PhysicsDptAngers/polyUAnalog/hardware/FX/img/PCM5102a.jpeg

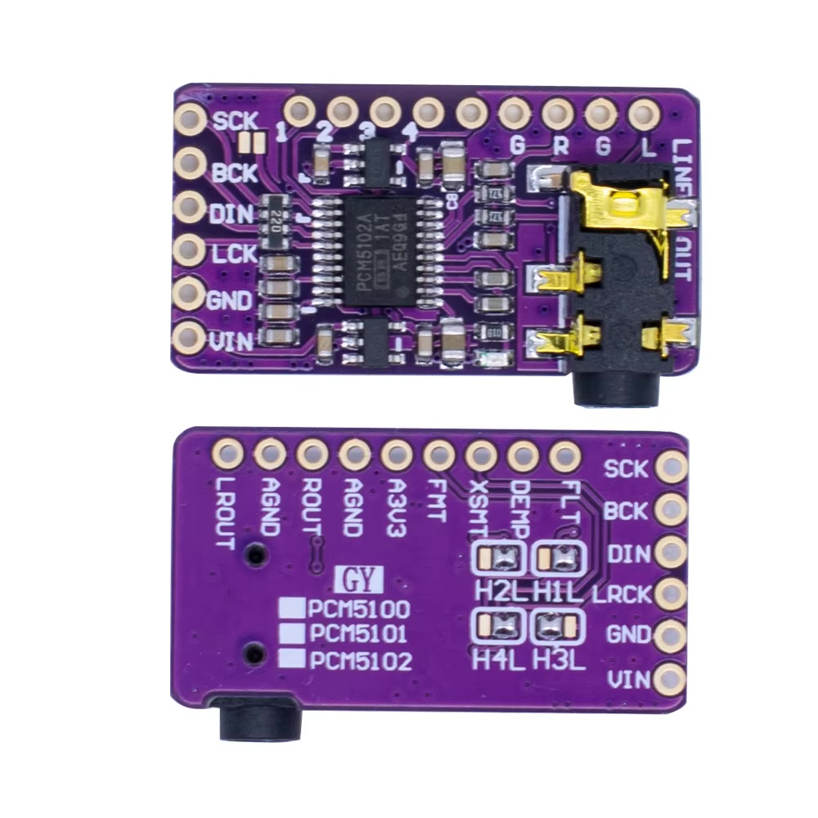
hardware/FX/img/PCM5102a.jpeg
