PhysicsDptAngers/polyUAnalog/hardware/voice/doc/img/Falstad_Balance_cv_level_shifter.png

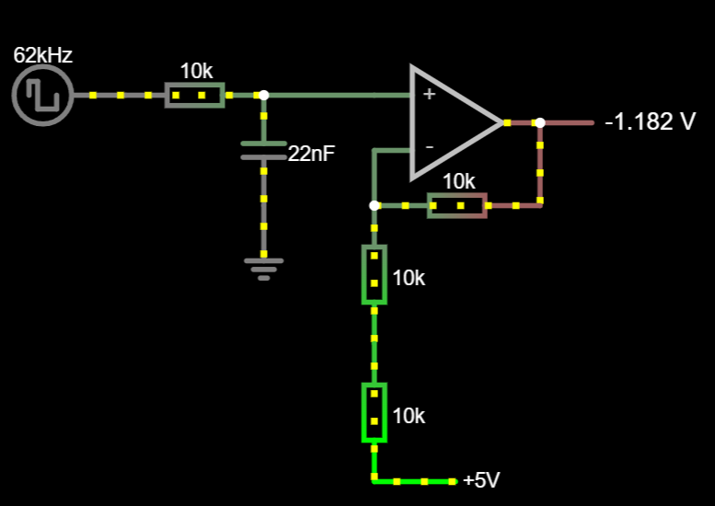
hardware/voice/doc/img/Falstad_Balance_cv_level_shifter.png
