PhysicsDptAngers/polyUAnalog/hardware/voice/doc/img/Wave_select_schematics.png

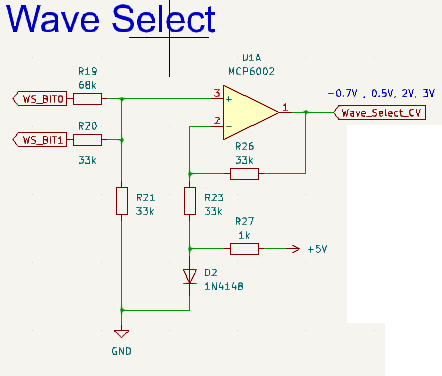
hardware/voice/doc/img/Wave_select_schematics.png
