PhysicsDptAngers/polyUAnalog/resources/conductor_board.png

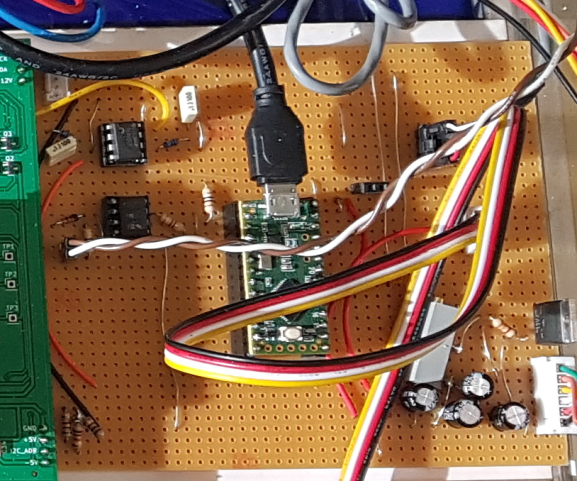
resources/conductor_board.png
