PhysicsDptAngers/polyUAnalog/resources/Photo_arch_main.png

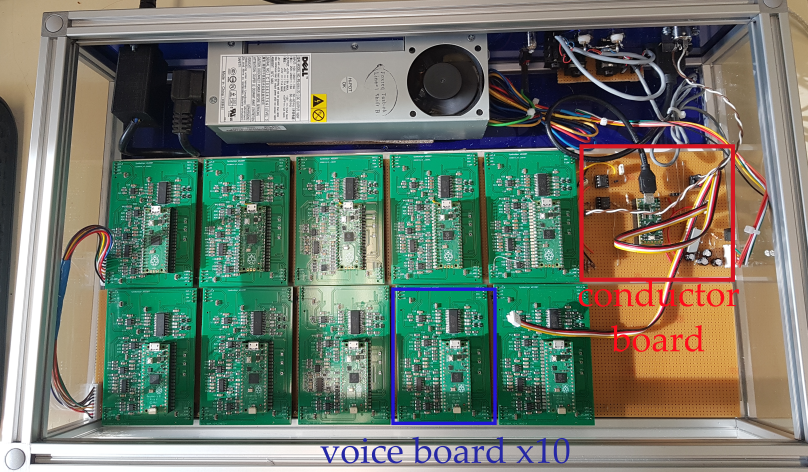
resources/Photo_arch_main.png
