PhysicsDptAngers/polyUAnalog/resources/photo_voice.png

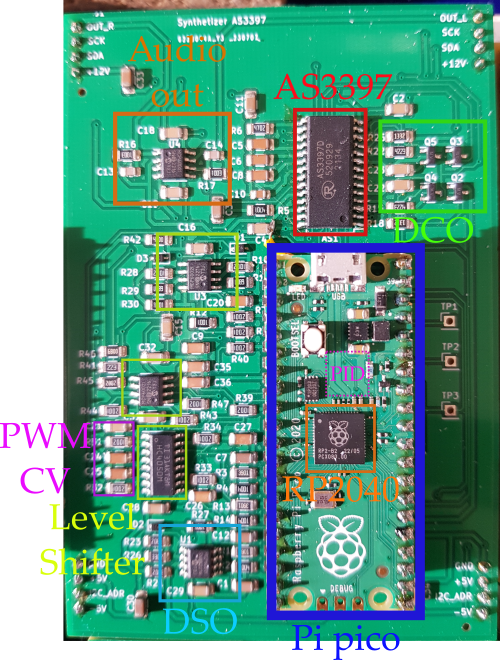
resources/photo_voice.png
