PhysicsDptAngers/polyUAnalog/resources/schema_AS3397.png

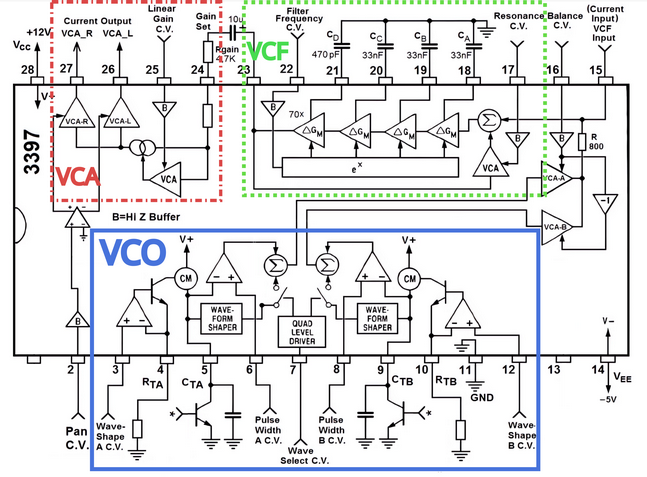
resources/schema_AS3397.png
