PhysicsDptAngers/polyUAnalog/resources/voice_archi.png

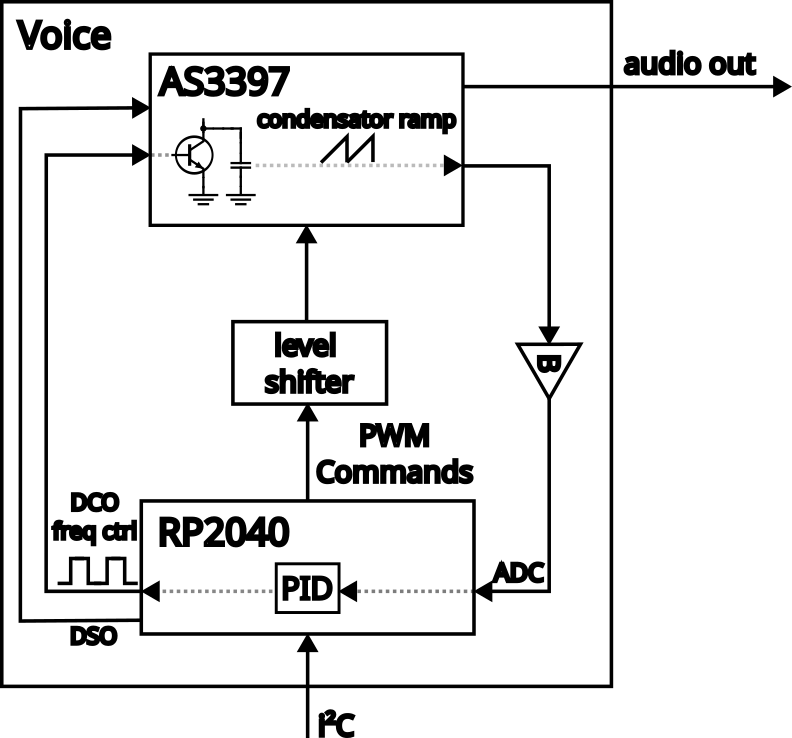
resources/voice_archi.png
