PhysicsDptAngers/polyUAnalog/firmware/conductor/preset.h

#ifndef PRESET_H
#define PRESET_H

//OSCILLATOR 1
#define OSC1WAVE 9
#define OSC1TRANSPOSE 10
#define OSC1PWM 11
#define OSC1DETUNE 18

//OSCILLATOR 2
#define OSC2WAVE 12
#define OSC2TRANSPOSE 13
#define OSC2DETUNE 14
#define OSC2PWM 15

//MIXER
#define BALANCE 16

//DSO
#define DSOWAVE 38
#define DSOTRANSPOSE 39
#define DSODETUNE 40
#define DSOPW 41
#define DSOMIX 42
#define MIXNOISE 44

//ENVELOPPE GENERATOR 1
#define EG1ATTACK 19
#define EG1DECAY 20
#define EG1SUSTAIN 21
#define EG1RELEASE 22
//ENVELOPPE GENERATOR 2
#define EG2ATTACK 23
#define EG2DECAY 24
#define EG2SUSTAIN 25
#define EG2RELEASE 26
#define EG22FREQ 51

//LOW PASS FILTER
#define FILTERFC 74
#define FILTERFCLOW 75
#define FILTERRES 27
#define FILTERKEY 28
#define FILTERENV 29
#define MODAMOUNT 37

//LOW FREQUENCY OSCILLATOR 1
#define LFO1WAVE 30
#define LFO1FREQ 31
#define LFO12PWA 35
#define LFO12PWB 36
#define LFO12FREQ 85
#define LFO12FILTER 86
#define LFO12PWDSO 43
#define LFO12PAN 45

//Velocity
#define VEL2VCA 46
#define VEL2FILTER 47

//Pan
#define KEY2PAN 48

//After Touch
#define AFT2VCA 49
#define AFT2FILTER 50

//GLOBAL PARAMETERS
#define GLBDETUNE 104
#define GLBTRANSPOSE 105
#define GLBVELOCITY 106
#define GLBVOLUME 7
#define GLBGLIDE 5
#define PAN 32

#define ALLSOUNDOFF 120
#define ALLNOTESOFF 123

// Definition of MIDI controller names
const char* controlleurNom[] = {
  "OSC1WAVE", "OSC1TRANSPOSE", "OSC1PWM", "OSC1DETUNE",
  "OSC2WAVE", "OSC2TRANSPOSE", "OSC2DETUNE", "OSC2PWM",
  "BALANCE",
  "DSOWAVE", "DSOTRANSPOSE", "DSODETUNE", "DSOPW", "DSOMIX", "MIXNOISE",
  "EG1ATTACK", "EG1DECAY", "EG1SUSTAIN", "EG1RELEASE",
  "EG2ATTACK", "EG2DECAY", "EG2SUSTAIN", "EG2RELEASE", "EG22FREQ",
  "FILTERFC", "FILTERFCLOW", "FILTERRES", "FILTERKEY", "FILTERENV", "MODAMOUNT",
  "LFO1WAVE", "LFO1FREQ", "LFO12PWA", "LFO12PWB", "LFO12FREQ", "LFO12FILTER", "LFO12PWDSO", "LFO12PAN",
  "VEL2VCA", "VEL2FILTER",
  "KEY2PAN",
  "AFT2VCA", "AFT2FILTER",
  "GLBDETUNE", "GLBTRANSPOSE", "GLBVELOCITY", "GLBVOLUME", "GLBGLIDE", "PAN"
};

// Setting MIDI controller numbers
const byte controlleurNum[] = {
  OSC1WAVE, OSC1TRANSPOSE, OSC1PWM, OSC1DETUNE,
  OSC2WAVE, OSC2TRANSPOSE, OSC2DETUNE, OSC2PWM,
  BALANCE,
  DSOWAVE, DSOTRANSPOSE, DSODETUNE, DSOPW, DSOMIX, MIXNOISE,
  EG1ATTACK, EG1DECAY, EG1SUSTAIN, EG1RELEASE,
  EG2ATTACK, EG2DECAY, EG2SUSTAIN, EG2RELEASE, EG22FREQ,
  FILTERFC, FILTERFCLOW, FILTERRES, FILTERKEY, FILTERENV, MODAMOUNT,
  LFO1WAVE, LFO1FREQ, LFO12PWA, LFO12PWB, LFO12FREQ, LFO12FILTER, LFO12PWDSO, LFO12PAN,
  VEL2VCA, VEL2FILTER,
  KEY2PAN,
  AFT2VCA, AFT2FILTER,
  GLBDETUNE, GLBTRANSPOSE, GLBVELOCITY, GLBVOLUME, GLBGLIDE, PAN
};

#define NBPARAM 102

//Preset format {MIDI_CONTROLEUR, Value, MIDI_CONTROLEUR, Value, ...}
const uint8_t Saw0[] = { OSC1WAVE, 1, OSC1TRANSPOSE, 64, OSC1PWM, 64, OSC1DETUNE, 64,
                         OSC2WAVE, 1, OSC2TRANSPOSE, 64, OSC2DETUNE, 64, OSC2PWM, 64,
                         BALANCE, 0,
                         DSOWAVE, 0, DSOTRANSPOSE, 64, DSODETUNE, 64, DSOPW, 64, DSOMIX, 0, MIXNOISE, 0,
                         EG1ATTACK, 1, EG1DECAY, 127, EG1SUSTAIN, 127, EG1RELEASE, 1,
                         EG2ATTACK, 1, EG2DECAY, 127, EG2SUSTAIN, 127, EG2RELEASE, 1, EG22FREQ, 0,
                         FILTERFCLOW, 63, FILTERFC, 106, FILTERRES, 63, FILTERKEY, 0, FILTERENV, 0, MODAMOUNT, 0,
                         LFO1WAVE, 0, LFO1FREQ, 16, LFO12PWA, 0, LFO12PWB, 0, LFO12FREQ, 0, LFO12FILTER, 0, LFO12PWDSO, 0, LFO12PAN, 0,
                         VEL2VCA, 127, VEL2FILTER, 0,
                         KEY2PAN, 0,
                         AFT2VCA, 0, AFT2FILTER, 0,
                         GLBDETUNE, 64, GLBTRANSPOSE, 64, GLBVELOCITY, 127, GLBVOLUME, 32, GLBGLIDE, 0, PAN, 64,
                         ALLSOUNDOFF, 1, ALLNOTESOFF, 0 };

const uint8_t Preset1[] = { OSC1WAVE, 0, OSC1TRANSPOSE, 64, OSC1PWM, 64, OSC1DETUNE, 64,
                            OSC2WAVE, 0, OSC2TRANSPOSE, 64, OSC2DETUNE, 65, OSC2PWM, 64,
                            BALANCE, 120, DSOWAVE, 0, DSOTRANSPOSE, 64, DSODETUNE, 64,
                            DSOPW, 64, DSOMIX, 0, MIXNOISE, 0, EG1ATTACK, 1,
                            EG1DECAY, 127, EG1SUSTAIN, 127, EG1RELEASE, 1, EG2ATTACK, 1,
                            EG2DECAY, 127, EG2SUSTAIN, 127, EG2RELEASE, 1, EG22FREQ, 0,
                            FILTERFC, 106, FILTERFCLOW, 63, FILTERRES, 4, FILTERKEY, 0,
                            FILTERENV, 0, MODAMOUNT, 0, LFO1WAVE, 0, LFO1FREQ, 30,
                            LFO12PWA, 57, LFO12PWB, 0, LFO12FREQ, 0, LFO12FILTER, 18,
                            LFO12PWDSO, 0, LFO12PAN, 6, VEL2VCA, 127, VEL2FILTER, 0,
                            KEY2PAN, 0, AFT2VCA, 0, AFT2FILTER, 0, GLBDETUNE, 64,
                            GLBTRANSPOSE, 64, GLBVELOCITY, 127, GLBVOLUME, 32, GLBGLIDE, 3, PAN, 64 };

const uint8_t Preset2[] = { OSC1WAVE, 1, OSC1TRANSPOSE, 64, OSC1PWM, 64, OSC1DETUNE, 64,
                            OSC2WAVE, 1, OSC2TRANSPOSE, 64, OSC2DETUNE, 65, OSC2PWM, 64,
                            BALANCE, 76, DSOWAVE, 0, DSOTRANSPOSE, 64, DSODETUNE, 64,
                            DSOPW, 64, DSOMIX, 0, MIXNOISE, 0, EG1ATTACK, 1,
                            EG1DECAY, 127, EG1SUSTAIN, 127, EG1RELEASE, 1, EG2ATTACK, 1,
                            EG2DECAY, 127, EG2SUSTAIN, 127, EG2RELEASE, 1, EG22FREQ, 0,
                            FILTERFC, 106, FILTERFCLOW, 63, FILTERRES, 17, FILTERKEY, 0,
                            FILTERENV, 0, MODAMOUNT, 0, LFO1WAVE, 0, LFO1FREQ, 15,
                            LFO12PWA, 0, LFO12PWB, 0, LFO12FREQ, 0, LFO12FILTER, 49,
                            LFO12PWDSO, 0, LFO12PAN, 14, VEL2VCA, 127, VEL2FILTER, 0,
                            KEY2PAN, 0, AFT2VCA, 0, AFT2FILTER, 0, GLBDETUNE, 64,
                            GLBTRANSPOSE, 64, GLBVELOCITY, 127, GLBVOLUME, 32, GLBGLIDE, 3, PAN, 64 };

const uint8_t Preset3[] = { OSC1WAVE, 0, OSC1TRANSPOSE, 64, OSC1PWM, 0, OSC1DETUNE, 64,
                            OSC2WAVE, 1, OSC2TRANSPOSE, 64, OSC2DETUNE, 65, OSC2PWM, 64,
                            BALANCE, 0, DSOWAVE, 0, DSOTRANSPOSE, 64, DSODETUNE, 64,
                            DSOPW, 64, DSOMIX, 0, MIXNOISE, 0, EG1ATTACK, 86,
                            EG1DECAY, 113, EG1SUSTAIN, 84, EG1RELEASE, 9, EG2ATTACK, 1,
                            EG2DECAY, 127, EG2SUSTAIN, 127, EG2RELEASE, 1, EG22FREQ, 0,
                            FILTERFC, 106, FILTERFCLOW, 63, FILTERRES, 22, FILTERKEY, 0,
                            FILTERENV, 0, MODAMOUNT, 0, LFO1WAVE, 0, LFO1FREQ, 25,
                            LFO12PWA, 96, LFO12PWB, 0, LFO12FREQ, 0, LFO12FILTER, 41,
                            LFO12PWDSO, 0, LFO12PAN, 0, VEL2VCA, 127, VEL2FILTER, 0,
                            KEY2PAN, 0, AFT2VCA, 0, AFT2FILTER, 0, GLBDETUNE, 64,
                            GLBTRANSPOSE, 64, GLBVELOCITY, 127, GLBVOLUME, 32, GLBGLIDE, 3, PAN, 64 };

const uint8_t Tri1[] = { OSC1WAVE, 2, OSC1TRANSPOSE, 52, OSC1PWM, 0, OSC1DETUNE, 64,
                         OSC2WAVE, 2, OSC2TRANSPOSE, 64, OSC2DETUNE, 66, OSC2PWM, 0,
                         BALANCE, 0, DSOWAVE, 0, DSOTRANSPOSE, 64, DSODETUNE, 64,
                         DSOPW, 64, DSOMIX, 0, MIXNOISE, 0, EG1ATTACK, 1,
                         EG1DECAY, 127, EG1SUSTAIN, 127, EG1RELEASE, 1, EG2ATTACK, 1,
                         EG2DECAY, 127, EG2SUSTAIN, 127, EG2RELEASE, 1, EG22FREQ, 0,
                         FILTERFC, 106, FILTERFCLOW, 63, FILTERRES, 4, FILTERKEY, 0,
                         FILTERENV, 0, MODAMOUNT, 0, LFO1WAVE, 0, LFO1FREQ, 16,
                         LFO12PWA, 0, LFO12PWB, 0, LFO12FREQ, 0, LFO12FILTER, 0,
                         LFO12PWDSO, 0, LFO12PAN, 0, VEL2VCA, 127, VEL2FILTER, 0,
                         KEY2PAN, 0, AFT2VCA, 0, AFT2FILTER, 0, GLBDETUNE, 64,
                         GLBTRANSPOSE, 64, GLBVELOCITY, 127, GLBVOLUME, 32, GLBGLIDE, 0, PAN, 64 };

const uint8_t Tri2[] = { OSC1WAVE, 3, OSC1TRANSPOSE, 64, OSC1PWM, 0, OSC1DETUNE, 64,
                         OSC2WAVE, 3, OSC2TRANSPOSE, 64, OSC2DETUNE, 66, OSC2PWM, 0,
                         BALANCE, 91, DSOWAVE, 0, DSOTRANSPOSE, 64, DSODETUNE, 64,
                         DSOPW, 64, DSOMIX, 0, MIXNOISE, 0, EG1ATTACK, 1,
                         EG1DECAY, 127, EG1SUSTAIN, 127, EG1RELEASE, 1, EG2ATTACK, 1,
                         EG2DECAY, 127, EG2SUSTAIN, 127, EG2RELEASE, 1, EG22FREQ, 0,
                         FILTERFC, 106, FILTERFCLOW, 63, FILTERRES, 4, FILTERKEY, 0,
                         FILTERENV, 0, MODAMOUNT, 0, LFO1WAVE, 0, LFO1FREQ, 16,
                         LFO12PWA, 0, LFO12PWB, 0, LFO12FREQ, 0, LFO12FILTER, 0,
                         LFO12PWDSO, 0, LFO12PAN, 0, VEL2VCA, 127, VEL2FILTER, 0,
                         KEY2PAN, 0, AFT2VCA, 0, AFT2FILTER, 0, GLBDETUNE, 64,
                         GLBTRANSPOSE, 64, GLBVELOCITY, 127, GLBVOLUME, 32, GLBGLIDE, 0, PAN, 64 };

const uint8_t Tri3[] = { OSC1WAVE, 4, OSC1TRANSPOSE, 64, OSC1PWM, 0, OSC1DETUNE, 64,
                         OSC2WAVE, 4, OSC2TRANSPOSE, 64, OSC2DETUNE, 66, OSC2PWM, 0,
                         BALANCE, 67, DSOWAVE, 0, DSOTRANSPOSE, 64, DSODETUNE, 64,
                         DSOPW, 64, DSOMIX, 0, MIXNOISE, 0, EG1ATTACK, 1,
                         EG1DECAY, 127, EG1SUSTAIN, 127, EG1RELEASE, 1, EG2ATTACK, 1,
                         EG2DECAY, 127, EG2SUSTAIN, 127, EG2RELEASE, 1, EG22FREQ, 0,
                         FILTERFC, 106, FILTERFCLOW, 63, FILTERRES, 4, FILTERKEY, 0,
                         FILTERENV, 0, MODAMOUNT, 0, LFO1WAVE, 0, LFO1FREQ, 16,
                         LFO12PWA, 0, LFO12PWB, 0, LFO12FREQ, 0, LFO12FILTER, 0,
                         LFO12PWDSO, 0, LFO12PAN, 0, VEL2VCA, 127, VEL2FILTER, 0,
                         KEY2PAN, 0, AFT2VCA, 0, AFT2FILTER, 0, GLBDETUNE, 64,
                         GLBTRANSPOSE, 64, GLBVELOCITY, 127, GLBVOLUME, 32, GLBGLIDE, 0, PAN, 64 };

const uint8_t Square1[] = { OSC1WAVE, 0, OSC1TRANSPOSE, 64, OSC1PWM, 127, OSC1DETUNE, 64,
                            OSC2WAVE, 0, OSC2TRANSPOSE, 64, OSC2DETUNE, 66, OSC2PWM, 127,
                            BALANCE, 127, DSOWAVE, 0, DSOTRANSPOSE, 64, DSODETUNE, 64,
                            DSOPW, 64, DSOMIX, 0, MIXNOISE, 0, EG1ATTACK, 1,
                            EG1DECAY, 127, EG1SUSTAIN, 127, EG1RELEASE, 1, EG2ATTACK, 1,
                            EG2DECAY, 127, EG2SUSTAIN, 127, EG2RELEASE, 1, EG22FREQ, 0,
                            FILTERFC, 106, FILTERFCLOW, 63, FILTERRES, 0, FILTERKEY, 0,
                            FILTERENV, 0, MODAMOUNT, 0, LFO1WAVE, 0, LFO1FREQ, 16,
                            LFO12PWA, 0, LFO12PWB, 0, LFO12FREQ, 0, LFO12FILTER, 0,
                            LFO12PWDSO, 0, LFO12PAN, 0, VEL2VCA, 127, VEL2FILTER, 0,
                            KEY2PAN, 0, AFT2VCA, 0, AFT2FILTER, 0, GLBDETUNE, 64,
                            GLBTRANSPOSE, 64, GLBVELOCITY, 127, GLBVOLUME, 32, GLBGLIDE, 0, PAN, 64 };

// Preset table
const uint8_t* Presets[] = { Saw0, Tri1, Tri2, Tri3, Square1, Preset1, Preset2, Preset3 /* Ajoutez d'autres tableaux de préréglages ici */ };
#endif
