PhysicsDptAngers/polyUAnalog/firmware/voice/as3397.h

#ifndef AS3397_H
#define AS3397_H

#include <math.h>
#include <hardware/gpio.h>
#include "hardware/pwm.h"
#include "hardware/adc.h"
#include "hardware/dma.h"
#include "pico/stdlib.h"
#include "hardware/pio.h"
#include "hardware/clocks.h"
#include "aspin.h"

#define PIDFIXE 1
#define ERROR_SUM_MAX 50000

const uint64_t srateFactor = 4294967296;
#if PIDFIXE == 1
const int64_t SCALE_FACTOR = 1 << 16;
#endif

const float MAXFREQ = 12544;
const float _div = 2;

const int CAPTURE_DEPTH = 100;
const float Fe = 1000000;

static int CAPTURE_CHANNEL = 0;
static uint16_t capture_buf[CAPTURE_DEPTH];
static uint dma_chan_adc;
static dma_channel_config cfg;

struct CallbackData {
  uint8_t WaveshapeFactor = 1;
  long SetPoint = WaveshapeFactor * 2.5 / convFactor;  // Initialise la consigne de l'asservissement à une amplitude de 2.5V
  long error = 0, output = 0;                          //Variables de la commande PI
  long errorSum[128] = {};
  uint8_t note;
#if PIDFIXE == 0
  float _Kp = 440 * Kp;
  float _Ki = Ki / 440;
#else
  int64_t _Kp = 440 * Kp * SCALE_FACTOR;
  int64_t _Ki = (Ki / 440) * SCALE_FACTOR;
#endif
  float noteFreq = 440;
  float noteDiv = 1;
  int64_t delay_us;
  uint32_t sliceH;
  uint32_t sliceL;
  uint32_t channelH;
  uint32_t channelL;
  int8_t Pwm;
  uint32_t PhaseAcc;
  uint32_t PhaseInc;

  long slope = 0;
  float Div = 0;
};

struct PWMsliceChannel {
  uint32_t slice;
  uint32_t channel;
  uint32_t dutyMax;
};


static struct CallbackData DcoA;
static struct CallbackData DcoB;
static struct CallbackData Dso;

uint8_t freqToMidiInt(float freq);
void measure_slope();

class As3397 {
private:
  struct PWMsliceChannel VWFA_MSB_CV_sliceNum;
  struct PWMsliceChannel VWFA_LSB_CV_sliceNum;
  struct PWMsliceChannel VWFB_MSB_CV_sliceNum;
  struct PWMsliceChannel VWFB_LSB_CV_sliceNum;
  struct PWMsliceChannel DSO_MSB_CV_sliceNum;
  struct PWMsliceChannel DSO_LSB_CV_sliceNum;
  struct PWMsliceChannel DCOA_PW_CV_sliceNum;
  struct PWMsliceChannel DCOB_PW_CV_sliceNum;
  struct PWMsliceChannel BALANCE_CV_sliceNum;
  struct PWMsliceChannel FILTER_FREQ_CV_sliceNum;
  struct PWMsliceChannel FILTER_RES_CV_sliceNum;
  struct PWMsliceChannel MOD_AMOUNT_CV_sliceNum;
  struct PWMsliceChannel VCA_CV_sliceNum;
  struct PWMsliceChannel PAN_CV_sliceNum;
  uint32_t dcosrate;
  uint offset;



public:
  As3397(uint32_t srate);
  struct PWMsliceChannel set_gpio_pwm(uint gpioCV, uint32_t resolution);
  void set_DcoA_freq(float freq);
  void set_DcoB_freq(float freq);
  void set_DcoAFM(float FMmod);
  void set_DcoBFM(float FMmod);
  void set_DcoA_pw_cv(int32_t level);
  void set_DcoB_pw_cv(int32_t level);
  void set_Balance_cv(int32_t level);
  void set_Mod_amount_cv(int32_t level);
  void set_Filter_freq_cv(int32_t level);
  void set_Filter_res_cv(int32_t level);
  void set_Vca_cv(int32_t level);
  void set_Pan_cv(int32_t level);

  void set_Wave_Select(uint8_t wave);
  void set_WaveshapeFactorDcoA(uint8_t waveshape);
  void set_WaveshapeFactorDcoB(uint8_t waveshape);

  void DSO(int32_t wave);

  void AdcDma_init();

  uint32_t getSliceDsoMSB() {
    return Dso.sliceH;
  };
  uint32_t getSliceDsoLSB() {
    return Dso.sliceL;
  };
  uint32_t getChannelDsoMSB() {
    return Dso.channelH;
  };
  uint32_t getChannelDsoLSB() {
    return Dso.channelL;
  };
};

#endif
