PhysicsDptAngers/polyUAnalog/firmware/voice/tables.h

#ifndef TABLES_H
#define TABLES_H

const int16_t tablogMidi[] = {
  1, 2, 3, 4, 5, 6, 7, 8, 9, 10, 12, 13, 14, 16, 17, 19, 20, 22, 24, 25, 27, 29, 31, 33, 35, 37, 39, 42, 44,
  46, 49, 52, 54, 57, 60, 63, 66, 70, 73, 77, 80, 84, 88, 92, 96, 101, 105, 110, 115, 120, 125, 131, 136,
  142, 148, 154, 161, 167, 174, 182, 189, 197, 205, 213, 222, 231, 240, 250, 260, 270, 281, 292, 303, 315, 327,
  340, 353, 367, 381, 396, 411, 427, 444, 461, 478, 496, 515, 535, 555, 576, 598, 621, 644, 668, 694, 720, 747,
  775, 804, 834, 865, 898, 931, 966, 1002, 1039, 1078, 1118, 1159, 1202, 1247, 1293, 1341, 1391, 1442, 1495,
  1551, 1608, 1667, 1729, 1792, 1858, 1927, 1998, 2071, 2147, 2226, 2308
};

const int8_t tabsin[] = {
  -1, 3, 6, 9, 12, 15, 18, 21, 24, 28,
  31, 34, 37, 40, 43, 46, 48, 51, 54, 57, 60, 63, 65, 68, 71, 73, 76, 78, 81, 83,
  85, 88, 90, 92, 94, 96, 98, 100, 102, 104, 106, 108, 109, 111, 112, 114, 115,
  117, 118, 119, 120, 121, 122, 123, 124, 124, 125, 126, 126, 127, 127, 127, 127,
  127, 127, 127, 127, 127, 127, 127, 126, 126, 125, 124, 124, 123, 122, 121, 120,
  119, 118, 117, 115, 114, 112, 111, 109, 108, 106, 104, 102, 100, 98, 96, 94, 92,
  90, 88, 85, 83, 81, 78, 76, 73, 71, 68, 65, 63, 60, 57, 54, 51, 48, 46, 43, 40,
  37, 34, 31, 28, 24, 21, 18, 15, 12, 9, 6, 3, 0, -4, -7, -10, -13, -16, -19, -22,
  -25, -29, -32, -35, -38, -41, -44, -47, -49, -52, -55, -58, -61, -64, -66, -69,
  -72, -74, -77, -79, -82, -84, -86, -89, -91, -93, -95, -97, -99, -101, -103,
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
  -55, -58, -61, -64, -66, -69, -72, -74, -77, -79, -82, -84, -86, -89, -91, -93,
  -95, -97, -99, -101, -103, -105, -107, -109, -110, -112, -113, -115, -116, -118,
  -119, -120, -121, -122, -123, -124, -125, -125, -126, -127, -127, -128, -128,
  -128, -128, -128
};


#endif
